idokar/MagicFlute/MagicFluteGame/images/helpBG.png

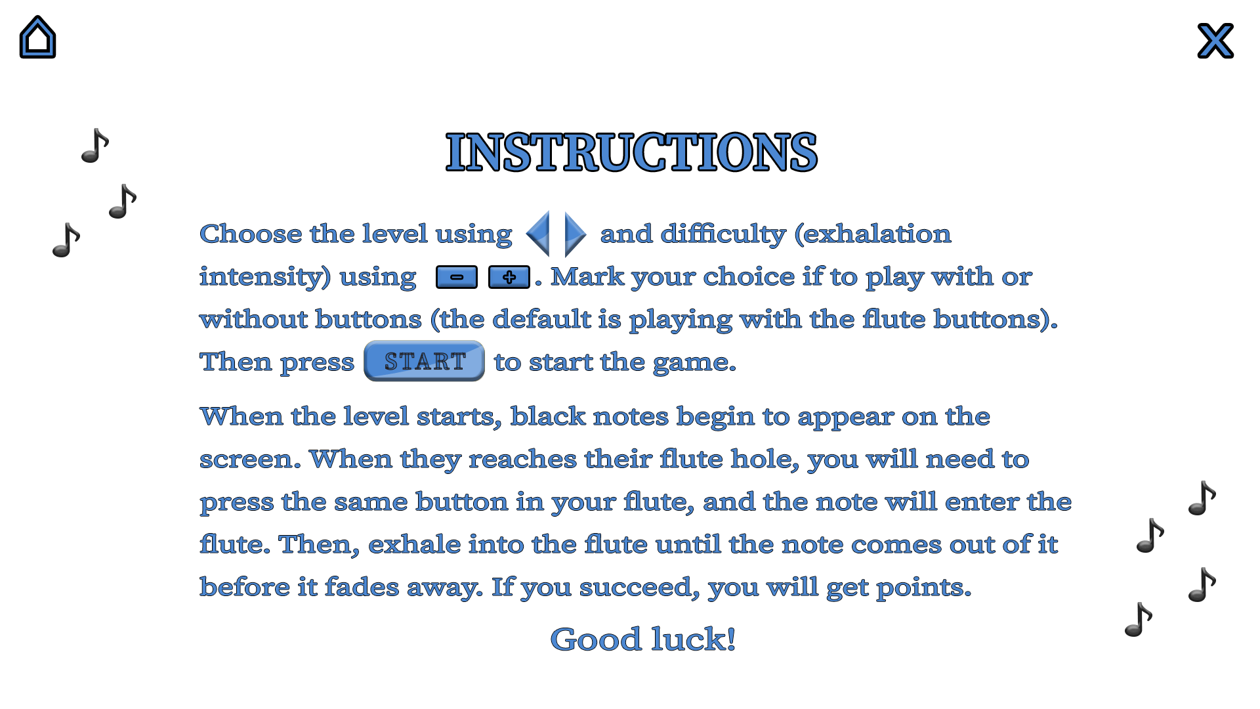
MagicFluteGame/images/helpBG.png
