idokar/MagicFlute/MagicFluteGame/images/popingNote.png

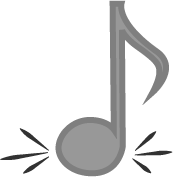
MagicFluteGame/images/popingNote.png
