idokar/MagicFlute/readme/fluteOpened.jpg

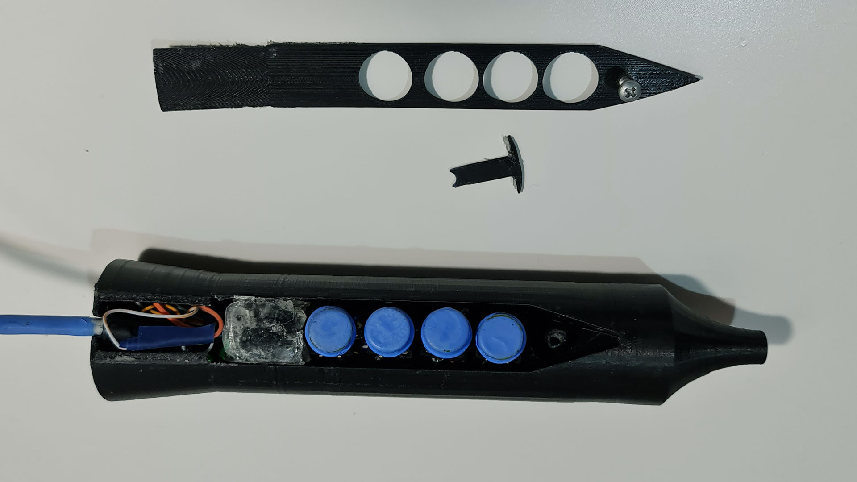
readme/fluteOpened.jpg
