idokar/MagicFlute/readme/openedBox.jpg

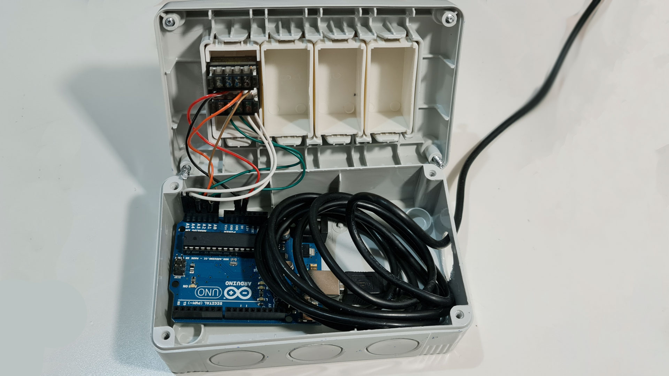
readme/openedBox.jpg
